ChocoEngine/hot-tea-stand/references/20260906_130759.jpg

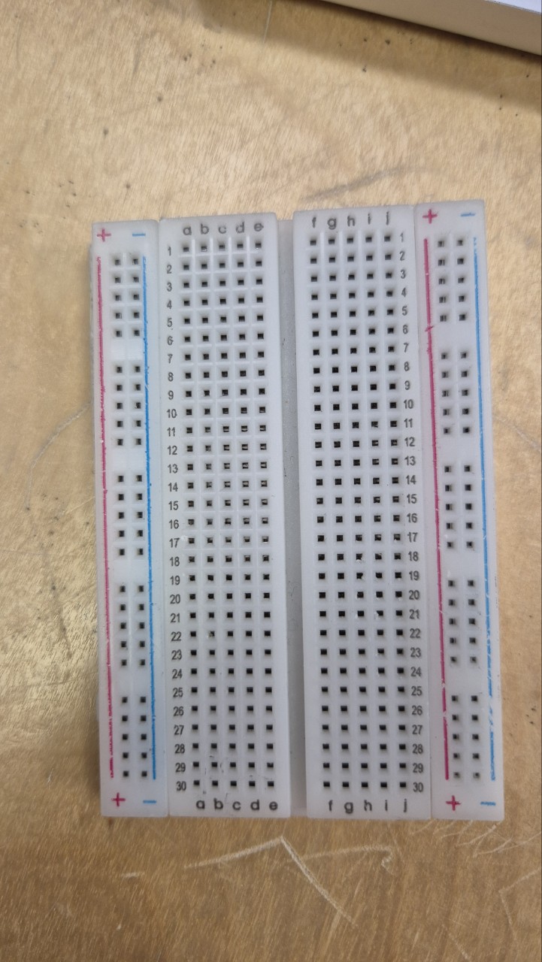
references/20260906_130759.jpg
