ChocoEngine/hot-tea-stand/references/20260906_133209.jpg

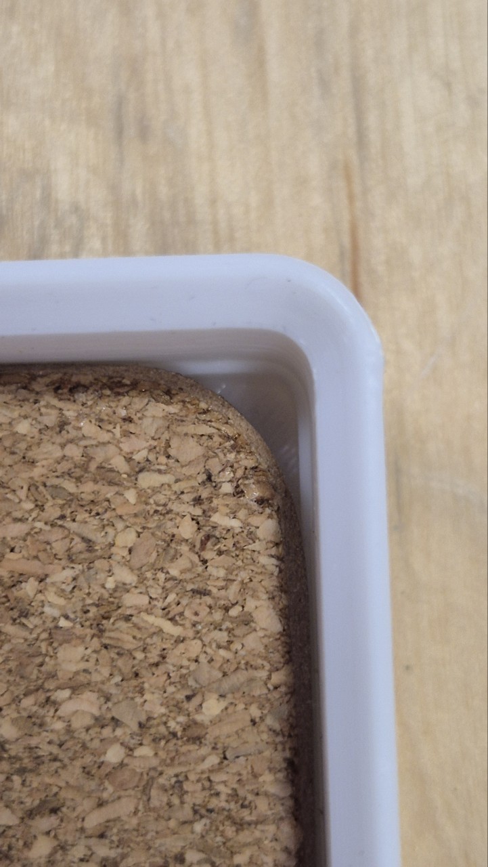
references/20260906_133209.jpg
